AnthonyDiGirolamo/teensy-display-shield/terminal_test/src/Colors.h

#pragma once

const uint32_t colors_endesga32[] = {
  0xbe4a2f,
  0xd77643,
  0xead4aa,
  0xe4a672,
  0xb86f50,
  0x733e39,
  0x3e2731,
  0xa22633,
  0xe43b44,
  0xf77622,
  0xfeae34,
  0xfee761,
  0x63c74d,
  0x3e8948,
  0x265c42,
  0x193c3e,
  0x124e89,
  0x0099db,
  0x2ce8f5,
  0xffffff,
  0xc0cbdc,
  0x8b9bb4,
  0x5a6988,
  0x3a4466,
  0x262b44,
  0x181425,
  0xff0044,
  0x68386c,
  0xb55088,
  0xf6757a,
  0xe8b796,
  0xc28569,
};
